reeshub/pc-sprint/ARTWRK2X.TOP.TIF

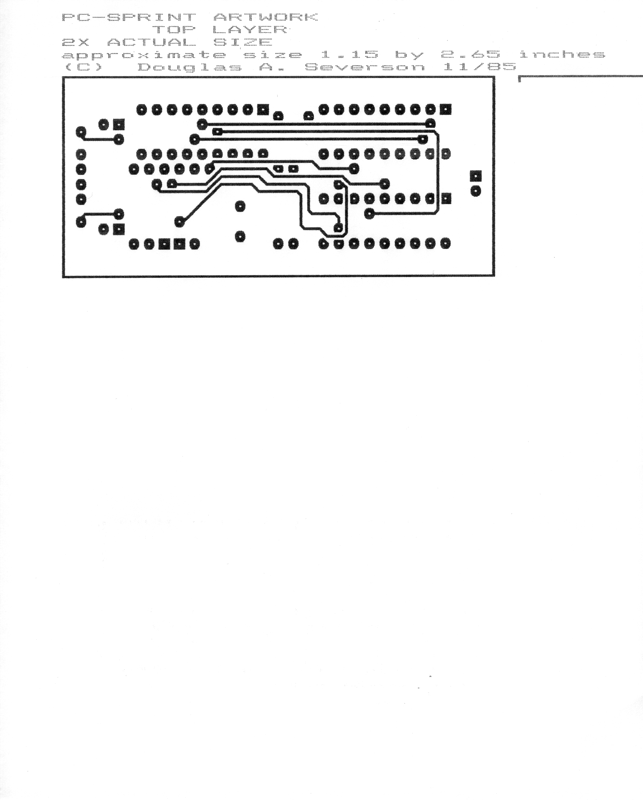
ARTWRK2X.TOP.TIF
