reeshub/pc-sprint/References/inmbolmie/breadboard.jpg

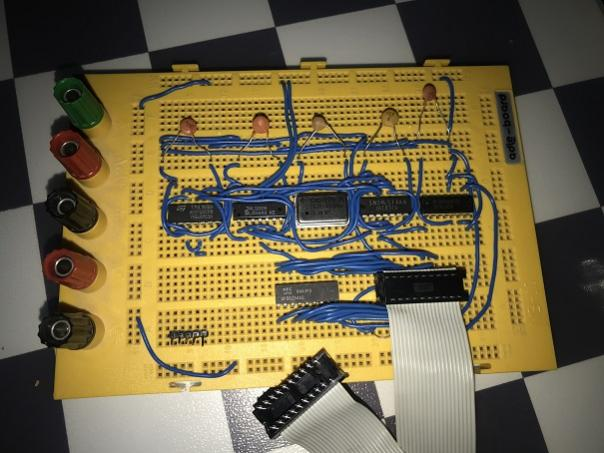
References/inmbolmie/breadboard.jpg
