reeshub/pc-sprint/References/inmbolmie/cable.jpg

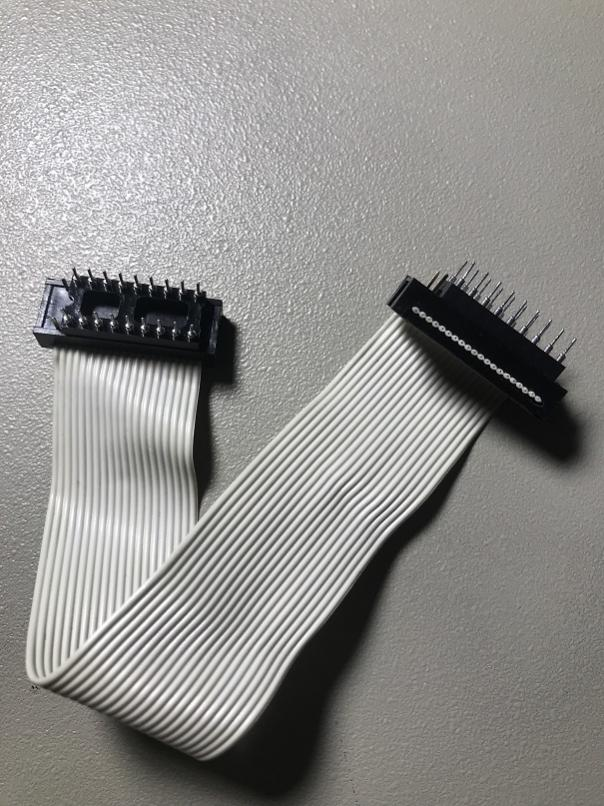
References/inmbolmie/cable.jpg
