reeshub/pc-sprint/References/inmbolmie/checkit.jpg

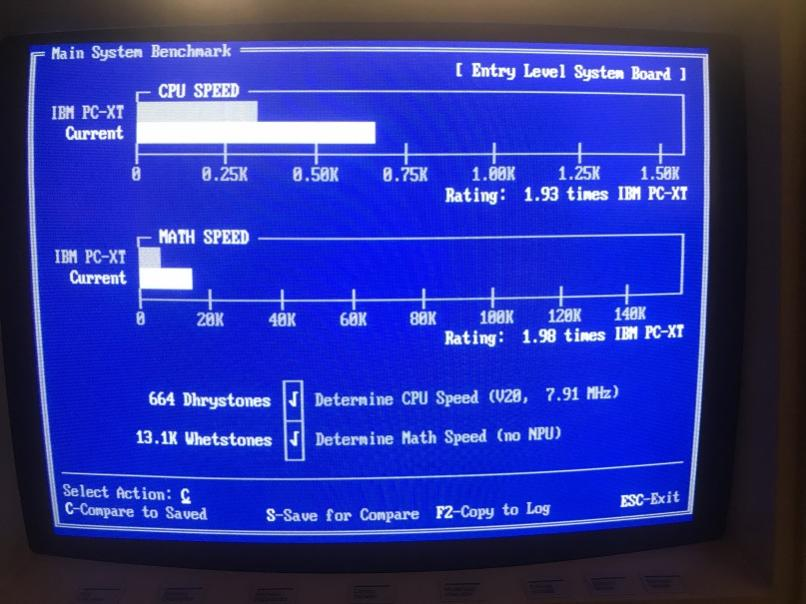
References/inmbolmie/checkit.jpg
