reeshub/pc-sprint/References/inmbolmie/general.jpg

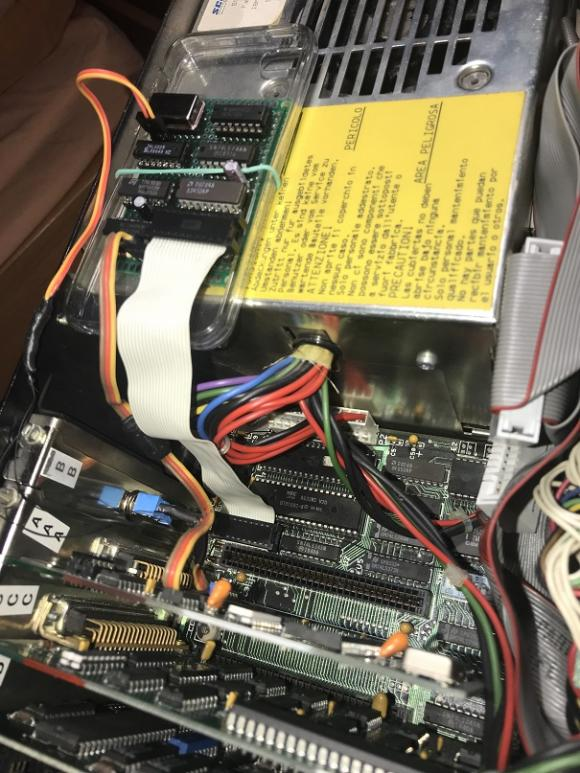
References/inmbolmie/general.jpg
