reeshub/pc-sprint/References/inmbolmie/mainboard_signals.jpg

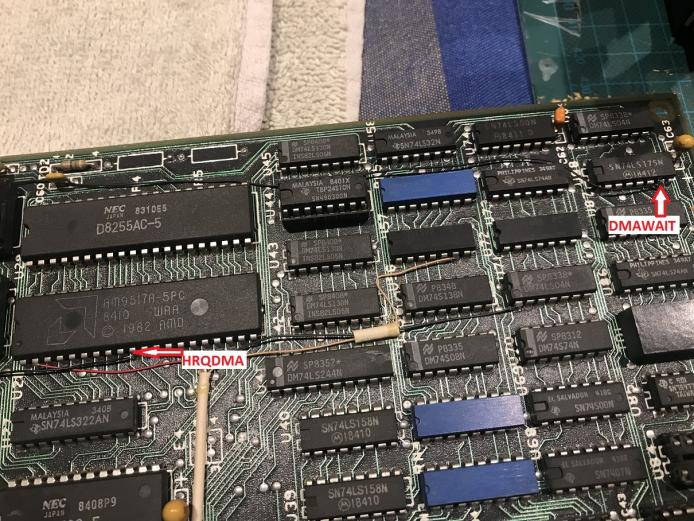
References/inmbolmie/mainboard_signals.jpg
