reeshub/pc-sprint/References/inmbolmie/prototype.jpg

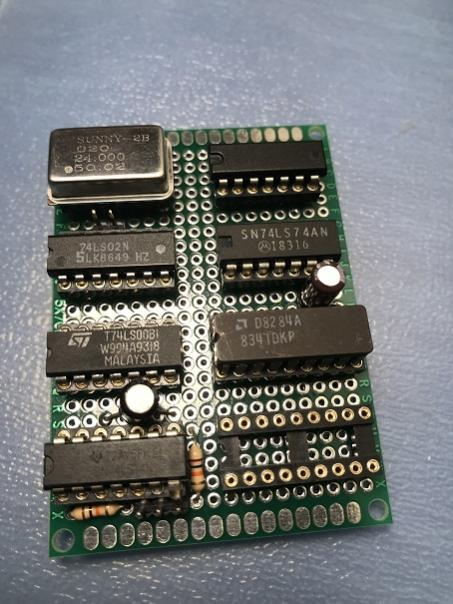
References/inmbolmie/prototype.jpg
