reeshub/pc-sprint/References/inmbolmie/prototype_back.jpg

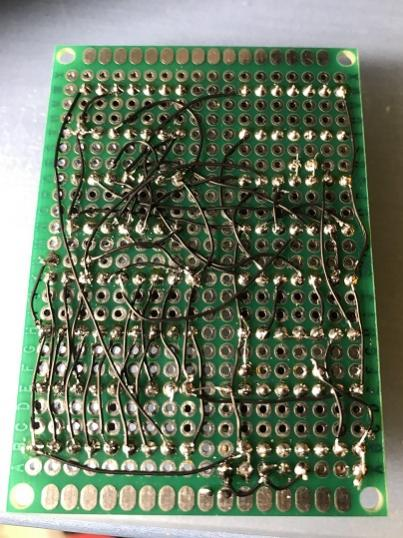
References/inmbolmie/prototype_back.jpg
