reeshub/pc-sprint/References/inmbolmie/sergey_prototype_pcb_rotated.jpg

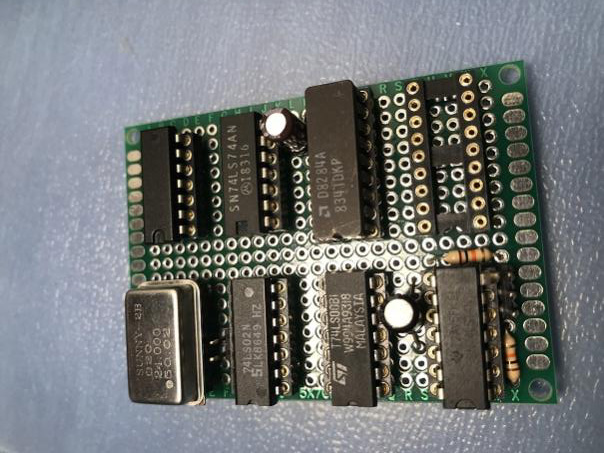
References/inmbolmie/sergey_prototype_pcb_rotated.jpg
