reeshub/pc-sprint/References/inmbolmie/socket.jpg

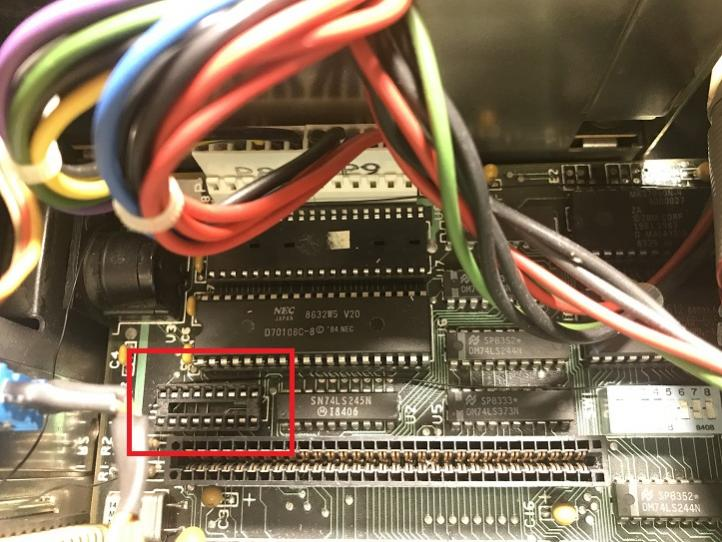
References/inmbolmie/socket.jpg
