reeshub/pc-sprint/References/inmbolmie/switch.jpg

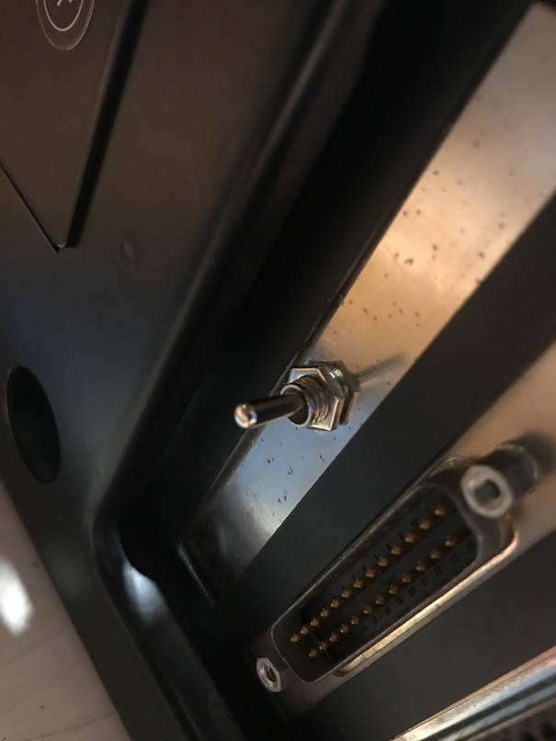
References/inmbolmie/switch.jpg
