reeshub/pc-sprint/Retro Canada/Images/pcsprint3.jpg

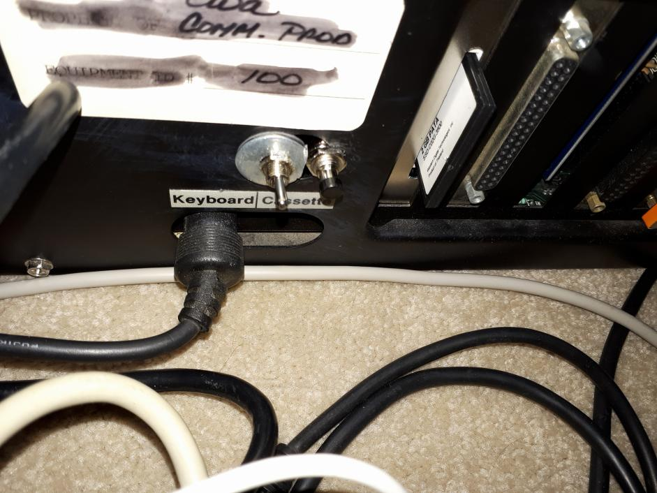
Retro Canada/Images/pcsprint3.jpg
