reeshub/pc-sprint/Retro Canada/Images/pcsprint4.jpg

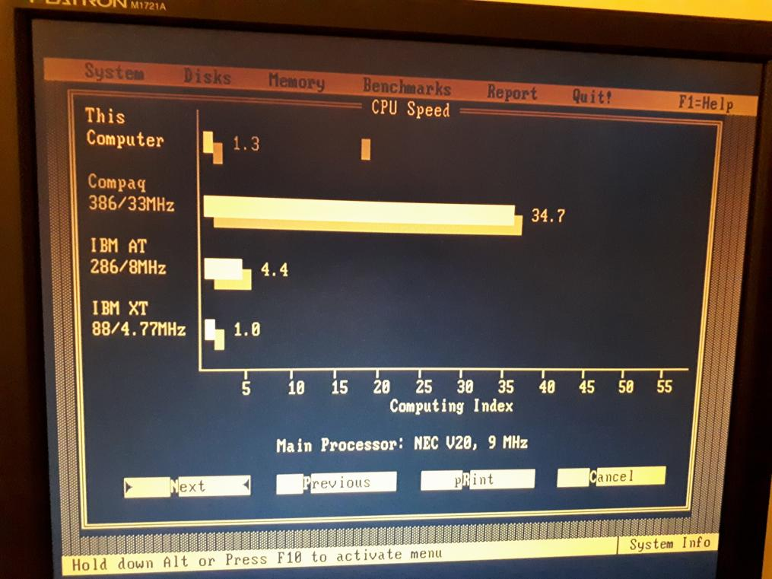
Retro Canada/Images/pcsprint4.jpg
