reeshub/pc-sprint/PC-SPRINT/PC-SPRINT/PC-SPRINT.sch

## KiCad design PC-SPRINT/PC-SPRINT/PC-SPRINT.sch (2020-03-10)

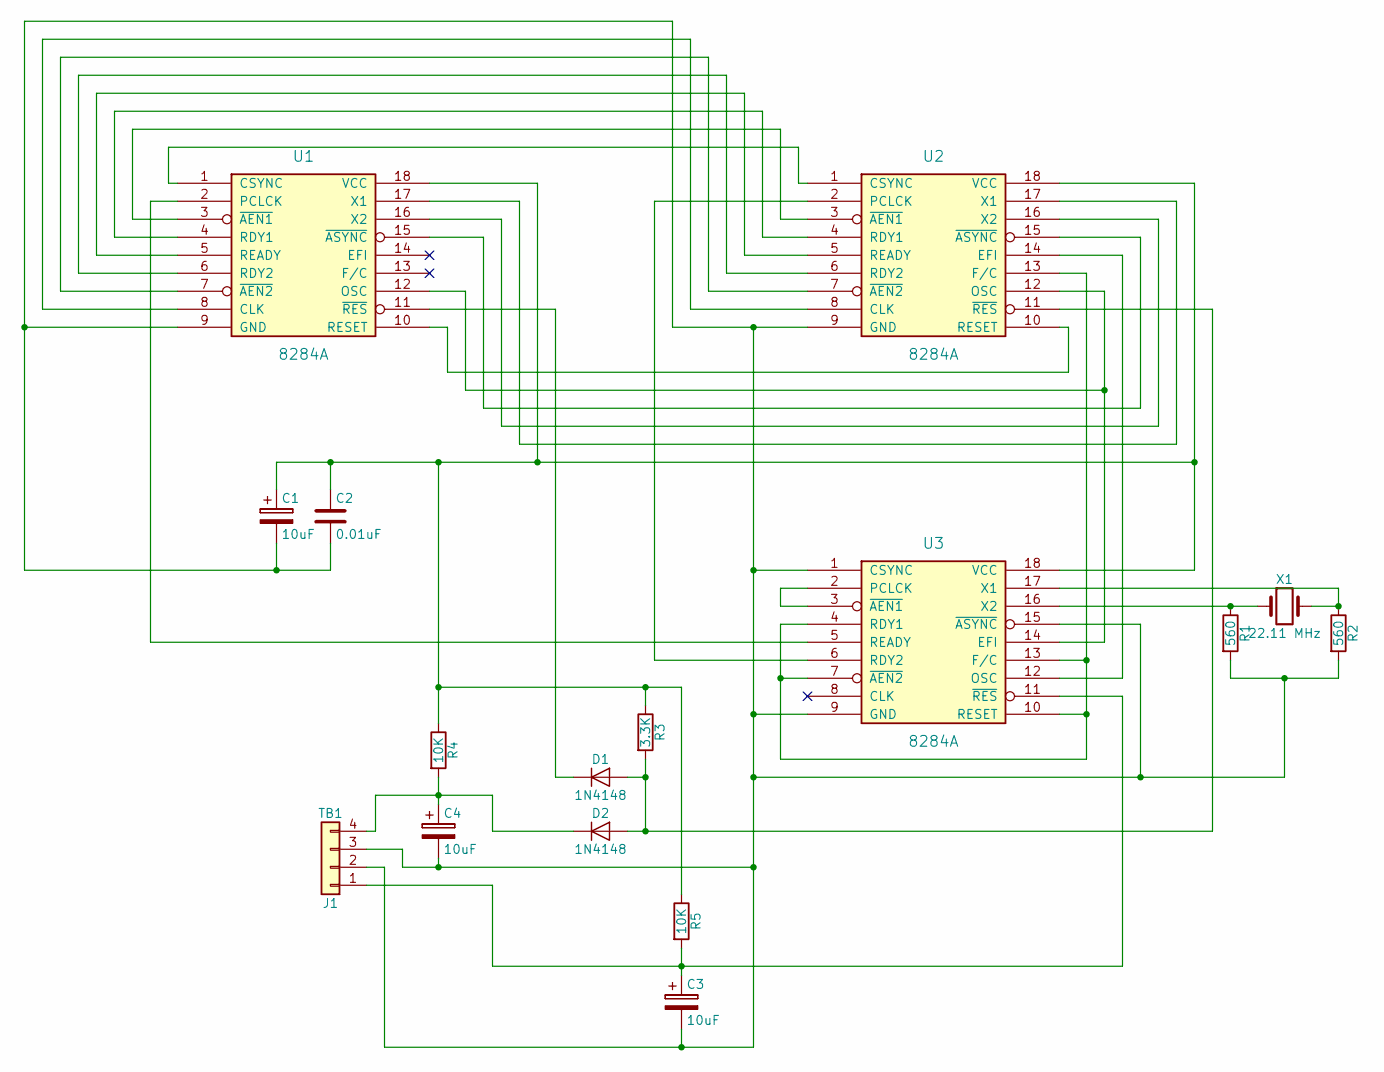
[picture p37: schematic PC-SPRINT.sch]

Parts:
C1, C3, C4: 10uF; CP_Radial_Tantal_D4.5mm_P2.50mm
C2: 0.01uF; C_Disc_D5.0mm_W2.5mm_P2.50mm
D1, D2: 1N4148; D_DO-35_SOD27_P7.62mm_Horizontal
J1: TB1; Pin_Header_Straight_1x04_Pitch2.54mm
R1, R2: 560; R_Axial_DIN0204_L3.6mm_D1.6mm_P7.62mm_Horizontal
R3: 3.3K; R_Axial_DIN0204_L3.6mm_D1.6mm_P7.62mm_Horizontal
R4, R5: 10K; R_Axial_DIN0204_L3.6mm_D1.6mm_P7.62mm_Horizontal
U1, U2, U3: 8284A; DIP-18_W7.62mm_LongPads
X1: 22.11 MHz; Crystal_HC18-U_Vertical

Connections:
unnamed: C1.1, C2.1, R3.1, R4.1, R5.1, U1.18 (VCC), U2.18 (VCC), U3.18 (VCC)
unnamed: C1.2, C2.2, C3.2, C4.2, J1.2, J1.3, R1.2, R2.2, U1.9 (GND), U2.9 (GND), U3.1 (CSYNC), U3.9 (GND), U3.15 (~ASYNC)
unnamed: C3.1, J1.1, R5.2, U3.11 (~RES)
unnamed: C4.1, D2.1 (K), J1.4, R4.2
unnamed: D1.1 (K), U1.11 (~RES)
unnamed: D1.2 (A), D2.2 (A), R3.2, U2.11 (~RES)
unnamed: R1.1, U3.16 (X2), X1.1
unnamed: R2.1, U3.17 (X1), X1.2
unnamed: U1.1 (CSYNC), U2.1 (CSYNC)
unnamed: U1.2 (PCLCK), U3.5 (READY)
unnamed: U1.3 (~AEN1), U2.3 (~AEN1)
unnamed: U1.4 (RDY1), U2.4 (RDY1)
unnamed: U1.5 (READY), U2.5 (READY)
unnamed: U1.6 (RDY2), U2.6 (RDY2)
unnamed: U1.7 (~AEN2), U2.7 (~AEN2)
unnamed: U1.8 (CLK), U2.8 (CLK)
unnamed: U1.10 (RESET), U2.10 (RESET)
unnamed: U1.12 (OSC), U2.12 (OSC), U3.14 (EFI)
unnamed: U1.15 (~ASYNC), U2.15 (~ASYNC)
unnamed: U1.16 (X2), U2.16 (X2)
unnamed: U1.17 (X1), U2.17 (X1)
unnamed: U2.2 (PCLCK), U3.6 (RDY2)
unnamed: U2.13 (F/C), U3.4 (RDY1), U3.7 (~AEN2), U3.10 (RESET), U3.13 (F/C)
unnamed: U2.14 (EFI), U3.12 (OSC)
unnamed: U3.2 (PCLCK), U3.3 (~AEN1)
